ellak-monades-aristeias/cityZEN/bench/3d model/φωτορεαλιστικη απεικονιση/render.47.jpg

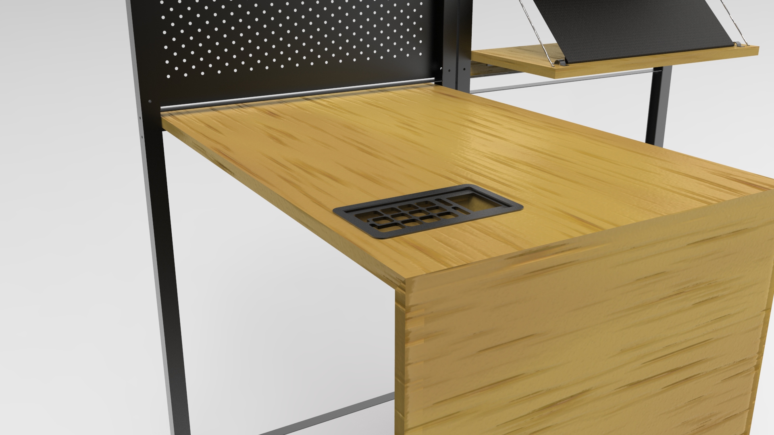
bench/3d model/φωτορεαλιστικη απεικονιση/render.47.jpg
