ellak-monades-aristeias/cityZEN/bench/3d model/φωτορεαλιστικη απεικονιση/render.51.jpg

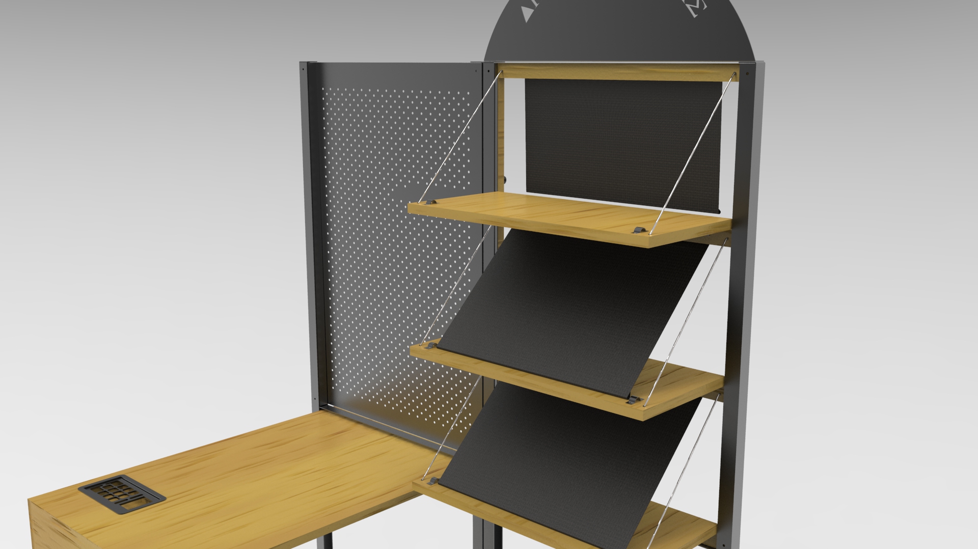
bench/3d model/φωτορεαλιστικη απεικονιση/render.51.jpg
