ellak-monades-aristeias/cityZEN/service/AA.png

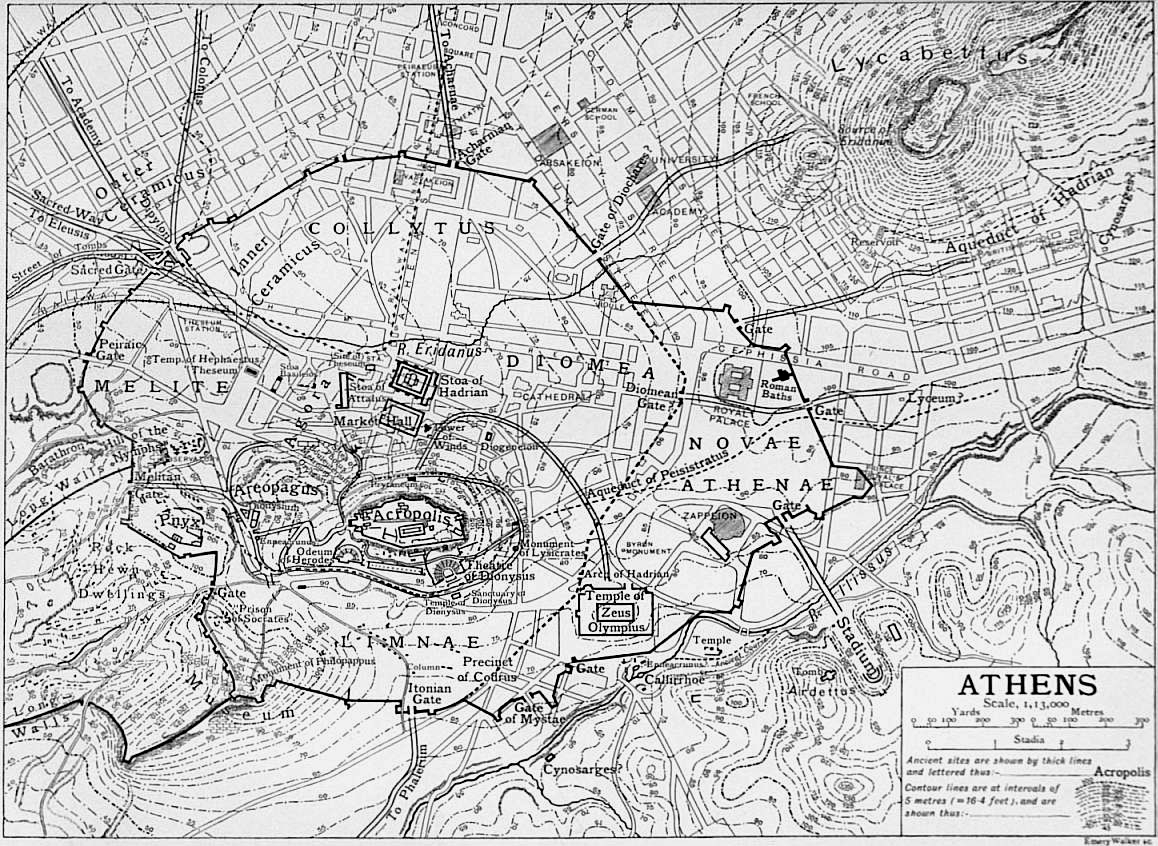
service/AA.png
